holmesrichards/herovco/Hardware/PCB_front/herovco_front/herovco_front.sch

## KiCad design Hardware/PCB_front/herovco_front/herovco_front.sch (2021-11-02)

Schematic: herovco_front.sch

Parts:
C101, C103, C104, C105, C109, C110: 100nF; C_Disc_D3.0mm_W1.6mm_P2.50mm
C102, C107, C108: 10nF; C_Rect_L7.2mm_W2.5mm_P5.00mm_FKS2_FKP2_MKS2_MKP2
C106: 1nF; C_Rect_L7.2mm_W2.5mm_P5.00mm_FKS2_FKP2_MKS2_MKP2
C111: 10nF; C_Disc_D3.0mm_W1.6mm_P2.50mm
D101: 1N4148; D_DO-35_SOD27_P7.62mm_Horizontal
D102: 1N4732A; D_DO-41_SOD81_P10.16mm_Horizontal
GRAF101: Holes; herovco_panel_holes
H101, H102, H103: MountingHole; MountingHole_3.2mm_M3
J101: 3_pin_Molex_header; Molex_KK-254_AE-6410-03A_1x03_P2.54mm_Vertical
J102: Conn_01x06; PinHeader_1x06_P2.54mm_Vertical
J103: Conn_01x09; PinHeader_1x09_P2.54mm_Vertical
J104: Conn_01x07; PinHeader_1x07_P2.54mm_Vertical
R101: 3M; R_Axial_DIN0207_L6.3mm_D2.5mm_P10.16mm_Horizontal
R102: 300k; R_Axial_DIN0207_L6.3mm_D2.5mm_P10.16mm_Horizontal
R103: 24k; R_Axial_DIN0207_L6.3mm_D2.5mm_P10.16mm_Horizontal
R104: 5.6k; R_Axial_DIN0207_L6.3mm_D2.5mm_P10.16mm_Horizontal
R105, R106, R107, R108, R111, R118, R119, R124, R126: 100k; R_Axial_DIN0207_L6.3mm_D2.5mm_P10.16mm_Horizontal
R109: 470k; R_Axial_DIN0207_L6.3mm_D2.5mm_P10.16mm_Horizontal
R110, R112, R125, R129: 10k; R_Axial_DIN0207_L6.3mm_D2.5mm_P10.16mm_Horizontal
R113: 1.8k; R_Axial_DIN0207_L6.3mm_D2.5mm_P10.16mm_Horizontal
R114: 1.5M; R_Axial_DIN0207_L6.3mm_D2.5mm_P10.16mm_Horizontal
R115: 470R; R_Axial_DIN0207_L6.3mm_D2.5mm_P10.16mm_Horizontal
R116, R117: 1M; R_Axial_DIN0207_L6.3mm_D2.5mm_P10.16mm_Horizontal
R120: 8.2k; R_Axial_DIN0207_L6.3mm_D2.5mm_P10.16mm_Horizontal
R121, R122: 1k; R_Axial_DIN0207_L6.3mm_D2.5mm_P10.16mm_Horizontal
R123: 240k; R_Axial_DIN0207_L6.3mm_D2.5mm_P10.16mm_Horizontal
R127: 47k; R_Axial_DIN0207_L6.3mm_D2.5mm_P10.16mm_Horizontal
R128: 20k; R_Axial_DIN0207_L6.3mm_D2.5mm_P10.16mm_Horizontal
RV101, RV103, RV104, RV110, RV111: 100k; Potentiometer_Alpha_RD901F-40-00D_Single_Vertical_centered
RV102, RV107: 10k; Potentiometer_Bourns_3296W_Vertical_screw_centered
RV105: 20k; Potentiometer_Bourns_3296W_Vertical_screw_centered
RV106: 100k; Potentiometer_Bourns_3296W_Vertical_screw_centered
RV108, RV109, RV113: 50k; Potentiometer_Bourns_3296W_Vertical_screw_centered
RV112: 5k; Potentiometer_Bourns_3296W_Vertical_screw_centered
SW101: SW_SPDT_MSM; SPDT-toggle-switch-1M-series
TP101: TestPoint; TestPoint_Pad_2.5x2.5mm
U101: TL074; DIP-14_W7.62mm_Socket_LongPads
U102: AS3340A; DIP-16_W7.62mm_Socket_LongPads
U103: TL072; DIP-8_W7.62mm_Socket_LongPads
U104: TL431LP; TO-92_Inline_Wide
U105: L79L05_TO92; TO-92_Inline_Wide

Notes on the sheet:
3340
CONTROL VOLTAGES
These resistors precision or hand matched
I did some tests that indicated 3M is better than 10M for suppressing high frequency oscillations, but in later tests 10M looked OK and 3M had a bad effect on minimum pulse width. I don't understand seeming inconsistency.
For VCC=12V, PWM_IN value for 100% PW is typically 4.0 V, maximum 4.3 V. With PWMIN=0, PULSE_WIDTH ±12 V becomes ∓5 V at op amp output. With PULSE_WIDTH=0, PWM_IN ±5 V becomes ∓5 V at op amp output. Either way LINK_OUT_PW becomes ±5 V. At top of trimmer V is 5.5 to 0 V. Adjust trimmer to get correc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
In Sidekick: LINK CV goes through 100k to CV_NODE (summed inside 3340) LINK FM goes through 10nF + 1M to LIN_FM (summed inside 3340) LINK PW goes through 100k to PWM summing amp (summed outside 3340) LINK SAW goes to SYNC
Can dispense with this op amp if there's a better use for it somewhere else
Regulated -5V is recommended by Alfa, and tests show it mostly or entirely suppresses PW frequency shift.
Use AS3340 or AS3340A. "AS3340A [has] much more output frequency stability against Vcc and VEE ....[and] benefits from improved symmetry of rising and falling edge of triangle signal (approx. 50%)."
-5V
HEADERS
Sin amplitude
Sine symmetry
Sine round
SINE TRIMMERS
+8V REFERENCE
