holmesrichards/herovco/Hardware/PCB_front/herovco_front/octave.sch

## KiCad design Hardware/PCB_front/herovco_front/octave.sch (2021-10-27)

Schematic: octave.sch

Parts:
J105: 3_pin_Molex_connector; Molex_KK-254_AE-6410-03A_1x03_P2.54mm_Vertical
R130, R131, R132, R133, R134, R135, R136, R137: 10k 1/8W; R_Axial_DIN0207_L6.3mm_D2.5mm_P10.16mm_Horizontal
SW102: SW_Rotary12; Rotary_Switch

Notes on the sheet:
Octave switch
Precision or hand matched resistors
OCTAVE SWITCH
Panel mounted
